Jerzeek/tinyPSU/img/tinyPSU_allComponents_Square.jpg

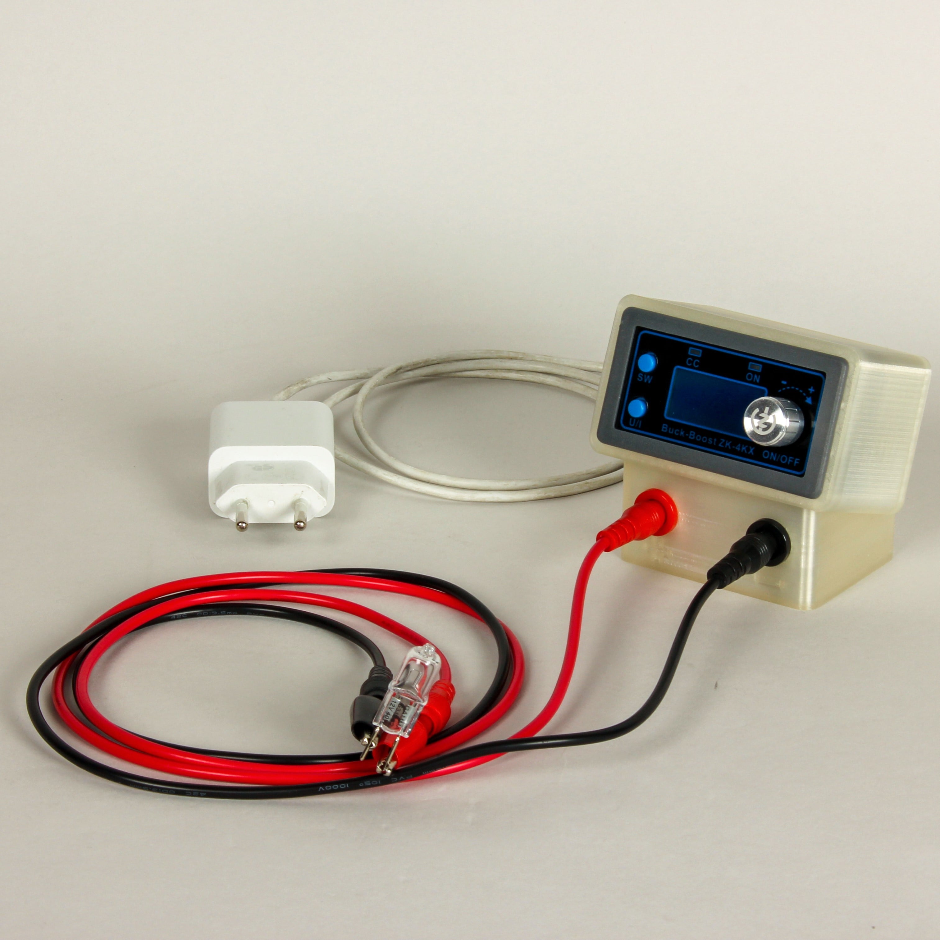
img/tinyPSU_allComponents_Square.jpg
